FIGLAB/High-Resolution-EIT/Firmware/Teensy_firmware/Multiplex_2pole.h

uint32_t abdcPortVectors8_2pole[] = {
	0,4,0,2,       //0 === 0 4 0 4
	0,1,0,1,       //1 === 0 8 0 8
	0,5,0,3,       //2 === 0 12 0 12
	0,2,32,0,       //3 === 0 16 0 16
	0,6,32,2,       //4 === 0 20 0 20
	0,3,32,1,       //5 === 0 24 0 24
	0,7,32,3,       //6 === 0 28 0 28
	0,524289,4,1,       //7 === 4 8 4 8
	0,524293,4,3,       //8 === 4 12 4 12
	0,524290,36,0,       //9 === 4 16 4 16
	0,524294,36,2,       //10 === 4 20 4 20
	0,524291,36,1,       //11 === 4 24 4 24
	0,524295,36,3,       //12 === 4 28 4 28
	16,262149,0,3,       //13 === 8 12 8 12
	16,262146,32,0,       //14 === 8 16 8 16
	16,262150,32,2,       //15 === 8 20 8 20
	16,262147,32,1,       //16 === 8 24 8 24
	16,262151,32,3,       //17 === 8 28 8 28
	16,786434,36,0,       //18 === 12 16 12 16
	16,786438,36,2,       //19 === 12 20 12 20
	16,786435,36,1,       //20 === 12 24 12 24
	16,786439,36,3,       //21 === 12 28 12 28
	32,6,160,2,       //22 === 16 20 16 20
	32,3,160,1,       //23 === 16 24 16 24
	32,7,160,3,       //24 === 16 28 16 28
	32,524291,164,1,       //25 === 20 24 20 24
	32,524295,164,3,       //26 === 20 28 20 28
	48,262151,160,3       //27 === 24 28 24 28
};

uint32_t abdcPortVectors16_2pole[] = {
	0,8,2,0,       //0 === 0 2 0 2
	0,4,0,2,       //1 === 0 4 0 4
	0,12,2,2,       //2 === 0 6 0 6
	0,1,0,1,       //3 === 0 8 0 8
	0,9,2,1,       //4 === 0 10 0 10
	0,5,0,3,       //5 === 0 12 0 12
	0,13,2,3,       //6 === 0 14 0 14
	0,2,32,0,       //7 === 0 16 0 16
	0,10,34,0,       //8 === 0 18 0 18
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
	4096,4,16,2,       //33 === 1 4 1 4
	4096,4,81,2,       //34 === 1 5 1 5
	4096,12,18,2,       //35 === 1 6 1 6
	4096,12,83,2,       //36 === 1 7 1 7
	4096,1,16,1,       //37 === 1 8 1 8
	4096,1,81,1,       //38 === 1 9 1 9
	4096,9,18,1,       //39 === 1 10 1 10
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
};
